SlightHeadache/choctopus44/images/choctopus44_usb_plug_collision.png

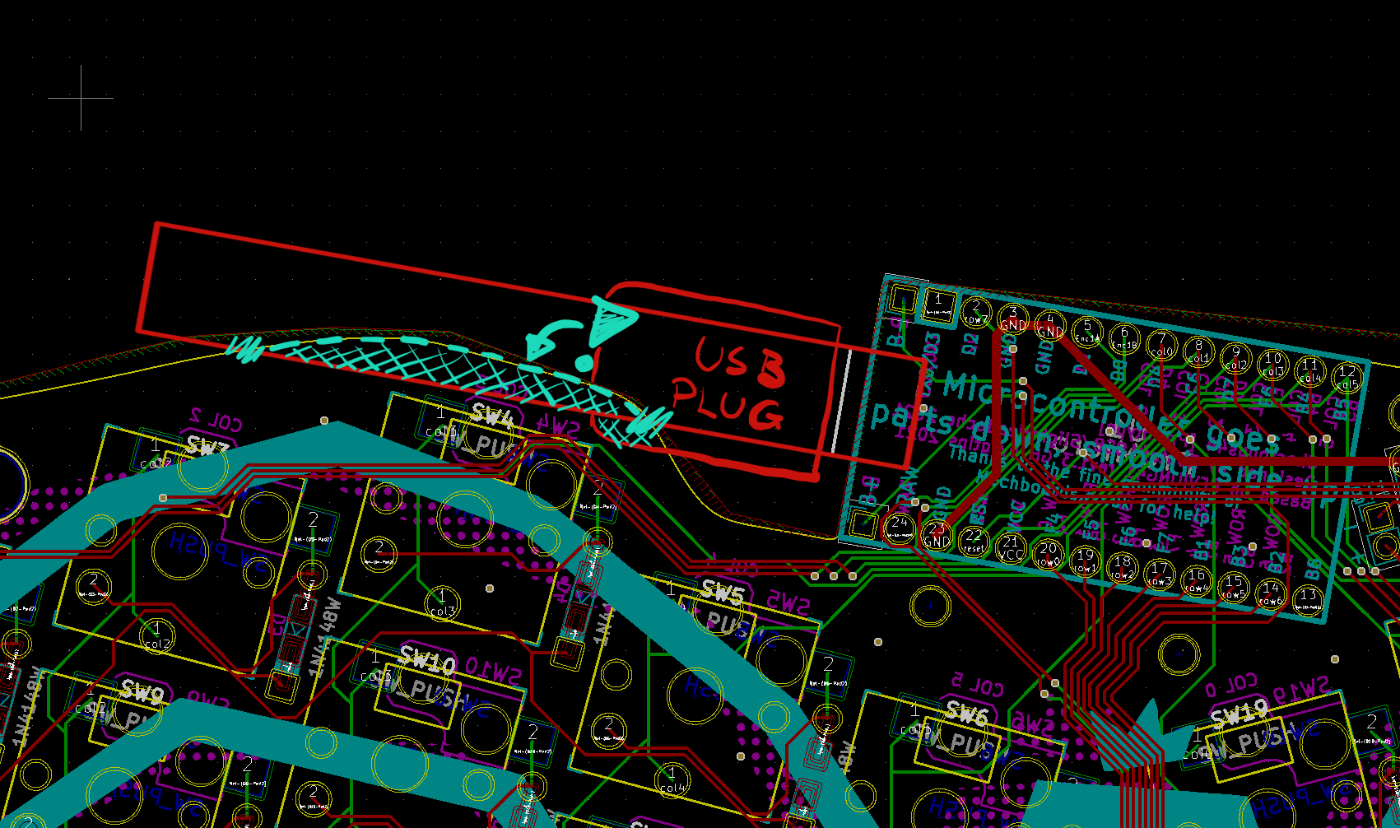
images/choctopus44_usb_plug_collision.png
